aneesharnavch/r00fu_Synth/Assets/Case_pic.png

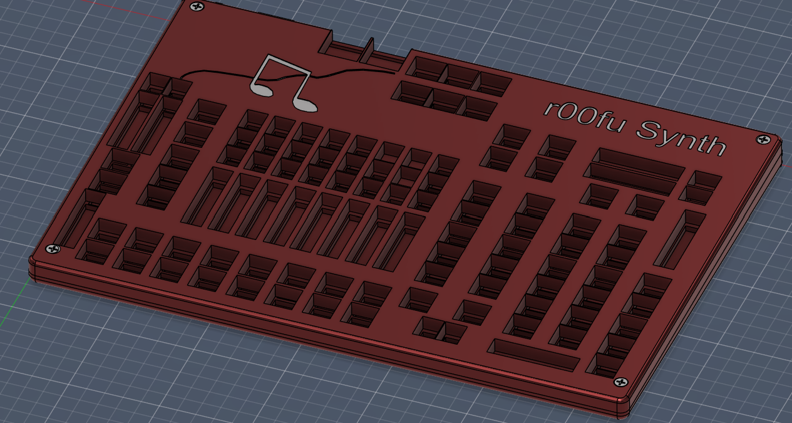
Assets/Case_pic.png
