aneesharnavch/r00fu_Synth/Assets/r00fuSynth_base.png

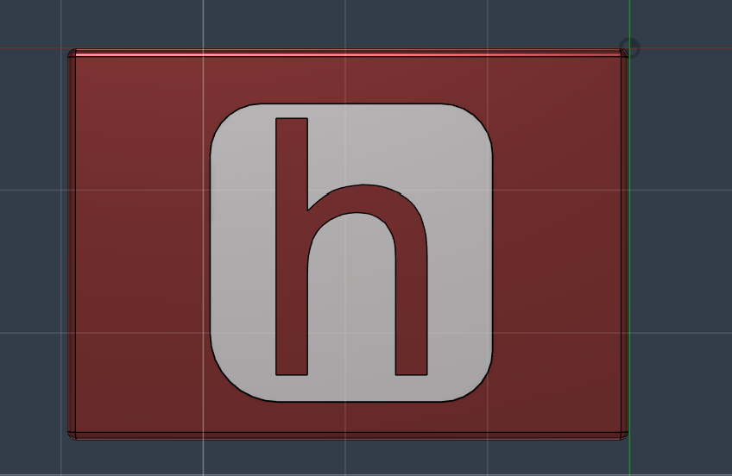
Assets/r00fuSynth_base.png
