aneesharnavch/r00fu_Synth/Assets/PCB_3D_Render_No_assembly_pic.png

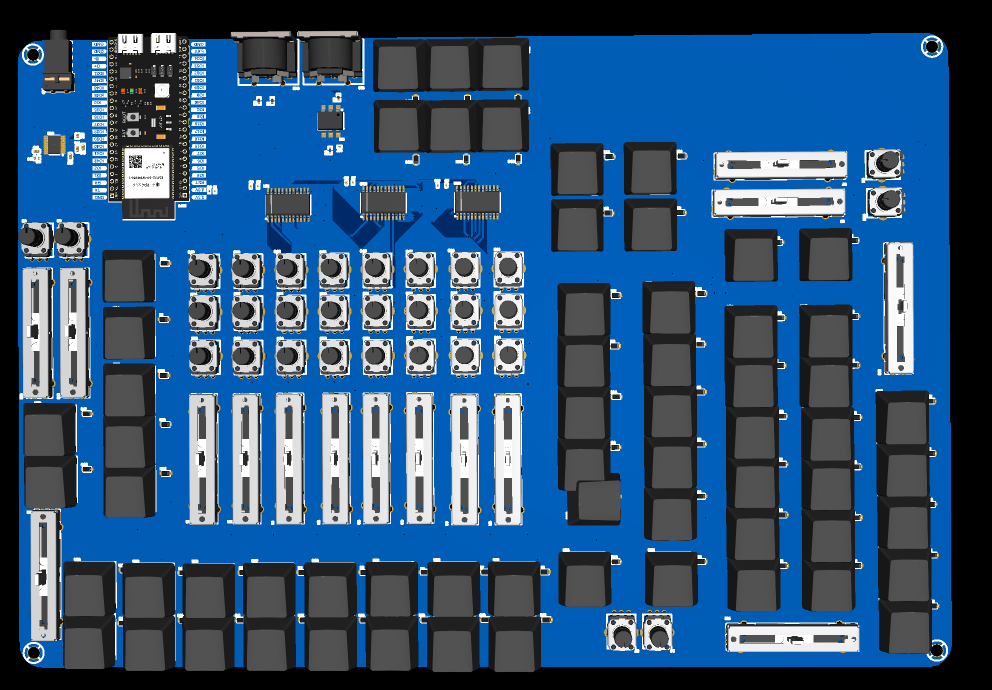
Assets/PCB_3D_Render_No_assembly_pic.png
