aneesharnavch/r00fu_Synth/Assets/r00fuSynth_Assembly.png

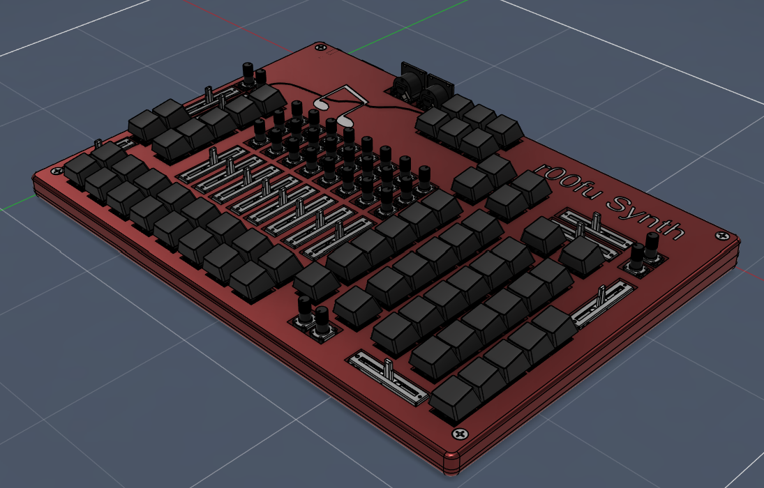
Assets/r00fuSynth_Assembly.png
