aneesharnavch/r00fu_Synth/Assets/r00fuSynth_Assembly_pic.png

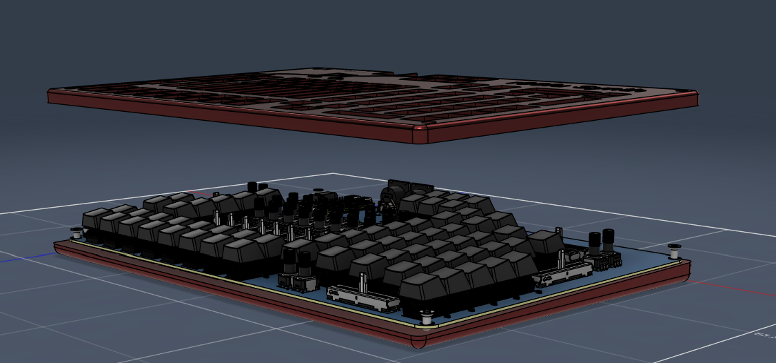
Assets/r00fuSynth_Assembly_pic.png
